ZeshuLiu/SX70z/Hardware/Body_controller/Case/贴片螺母M2.5-H3.5-D3.SLDPRT

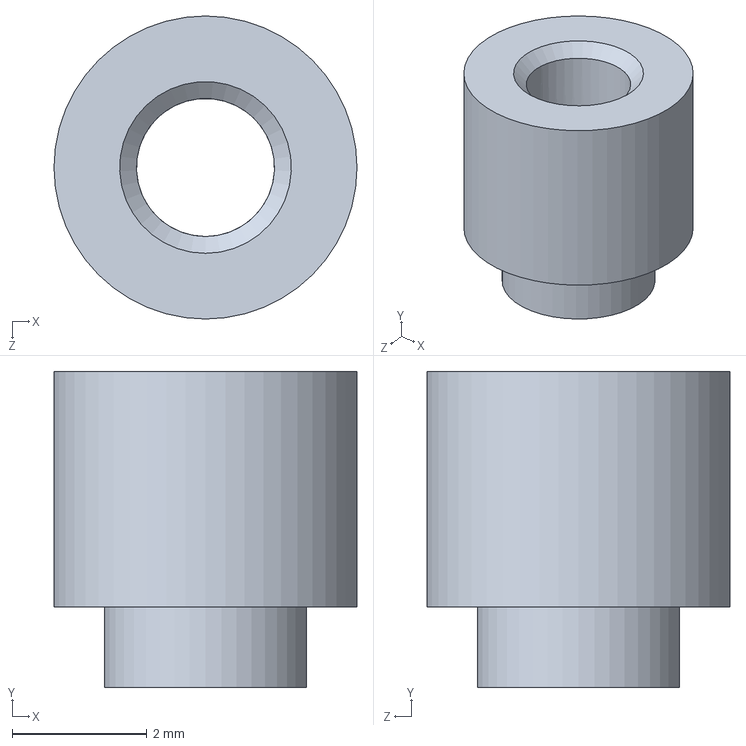
[picture p16: CAD file, 2026-05-23]
Hardware/Body_controller/Case/贴片螺母M2.5-H3.5-D3.SLDPRT
4.50 x 4.70 x 4.50 mm
