ZeshuLiu/SX70z/Hardware/MainController/SX70z_Normal/DXFs/SX70z_Normal-In1_Cu.dxf

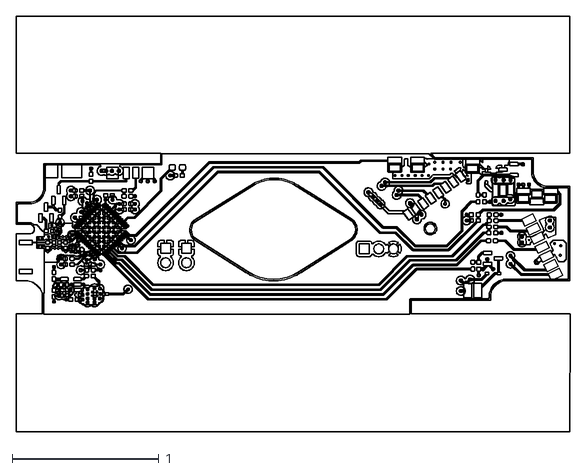
[picture p17: CAD file, 2026-05-23]
Hardware/MainController/SX70z_Normal/DXFs/SX70z_Normal-In1_Cu.dxf
3.78 x 2.83
