ZeshuLiu/SX70z/Hardware/Body_controller/Case/大头拨轮.SLDPRT

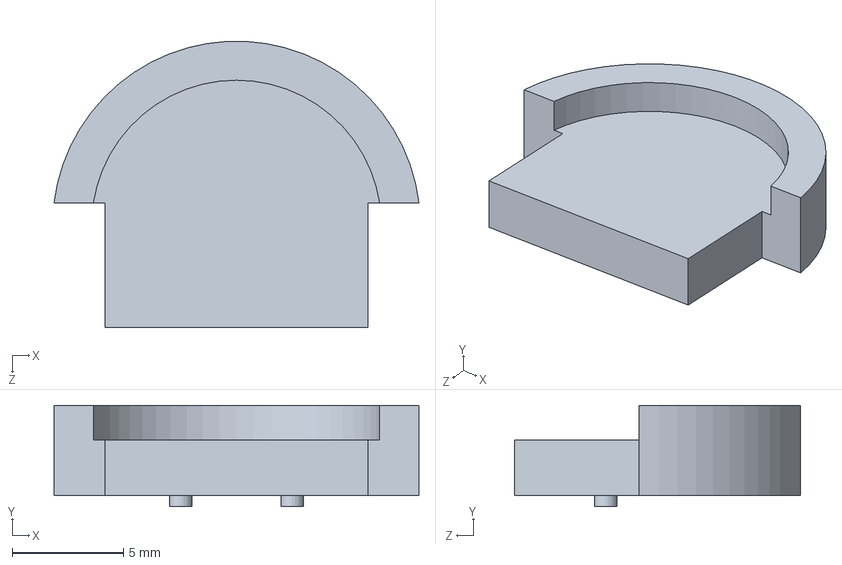
[picture p18: CAD file, 2026-05-23]
Hardware/Body_controller/Case/大头拨轮.SLDPRT
16.4 x 4.55 x 12.8 mm
