ZeshuLiu/SX70z/Hardware/MainController/SX70z_Normal/DXFs/SX70z_Normal-Edge_Cuts.dxf

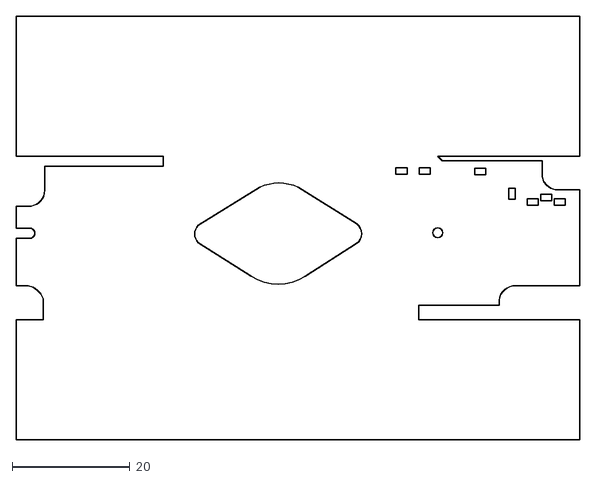
[picture p19: CAD file, 2026-05-23]
Hardware/MainController/SX70z_Normal/DXFs/SX70z_Normal-Edge_Cuts.dxf
95.9 x 72.0
