ZeshuLiu/SX70z/Hardware/Body_controller/Case/垫片.SLDPRT

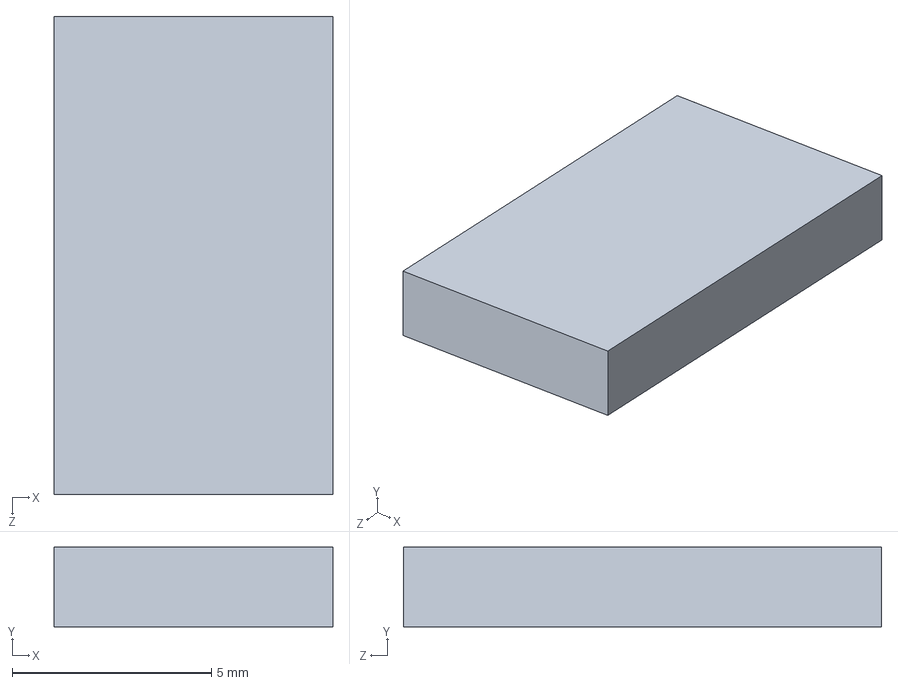
[picture p20: CAD file, 2026-05-23]
Hardware/Body_controller/Case/垫片.SLDPRT
7.00 x 2.00 x 12.0 mm
